Reid-n0rc/ADS-B_LNA_Project/LNA/Test_Data/ADSB_LNA_v2.png

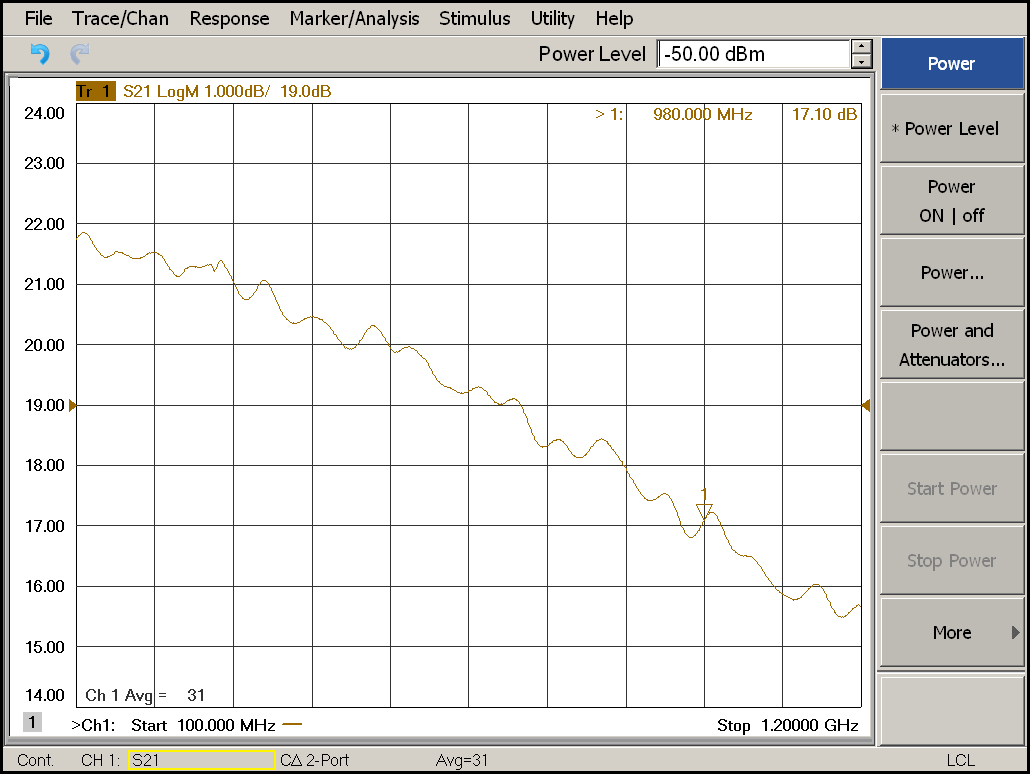
LNA/Test_Data/ADSB_LNA_v2.png
